olehbohdan/PrinterMonitor/images/ShaperResults/X/IMG_0770.JPG

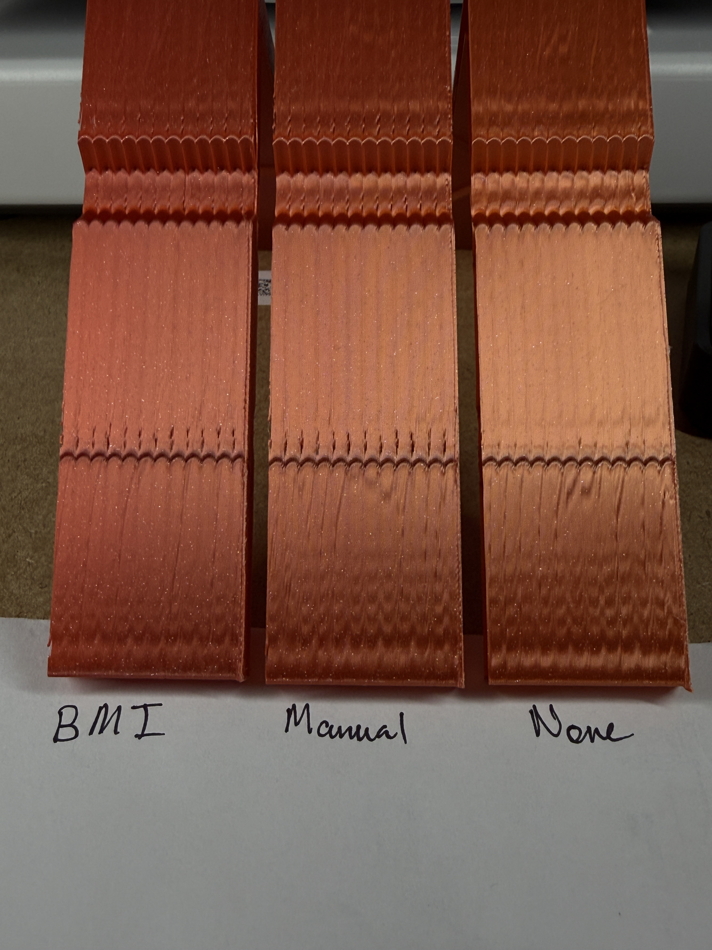
images/ShaperResults/X/IMG_0770.JPG
