olehbohdan/PrinterMonitor/images/ShaperResults/X/IMG_0772.JPG

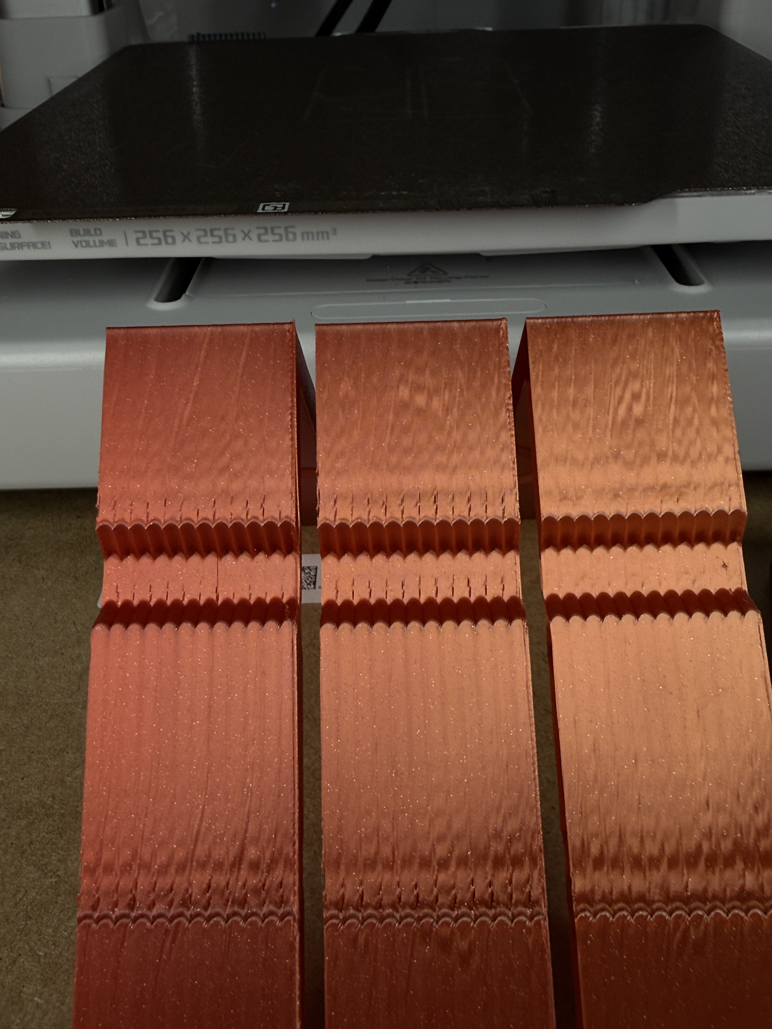
images/ShaperResults/X/IMG_0772.JPG
