olehbohdan/PrinterMonitor/images/ShaperResults/Y/IMG_0774.JPG

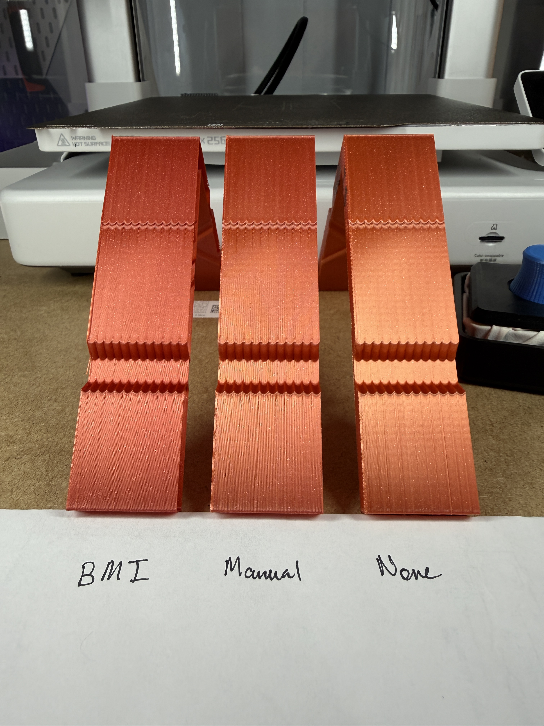
images/ShaperResults/Y/IMG_0774.JPG
