olehbohdan/PrinterMonitor/images/ShaperResults/Y/IMG_0775.JPG

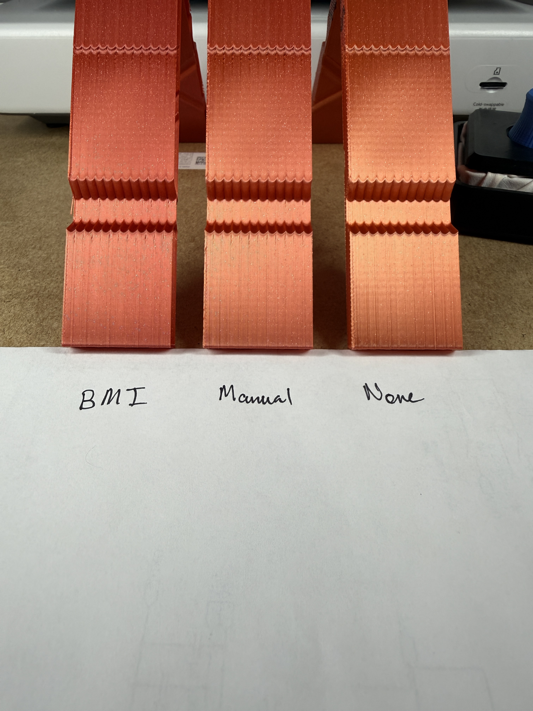
images/ShaperResults/Y/IMG_0775.JPG
