olehbohdan/PrinterMonitor/images/ShaperResults/Y/IMG_0776.JPG

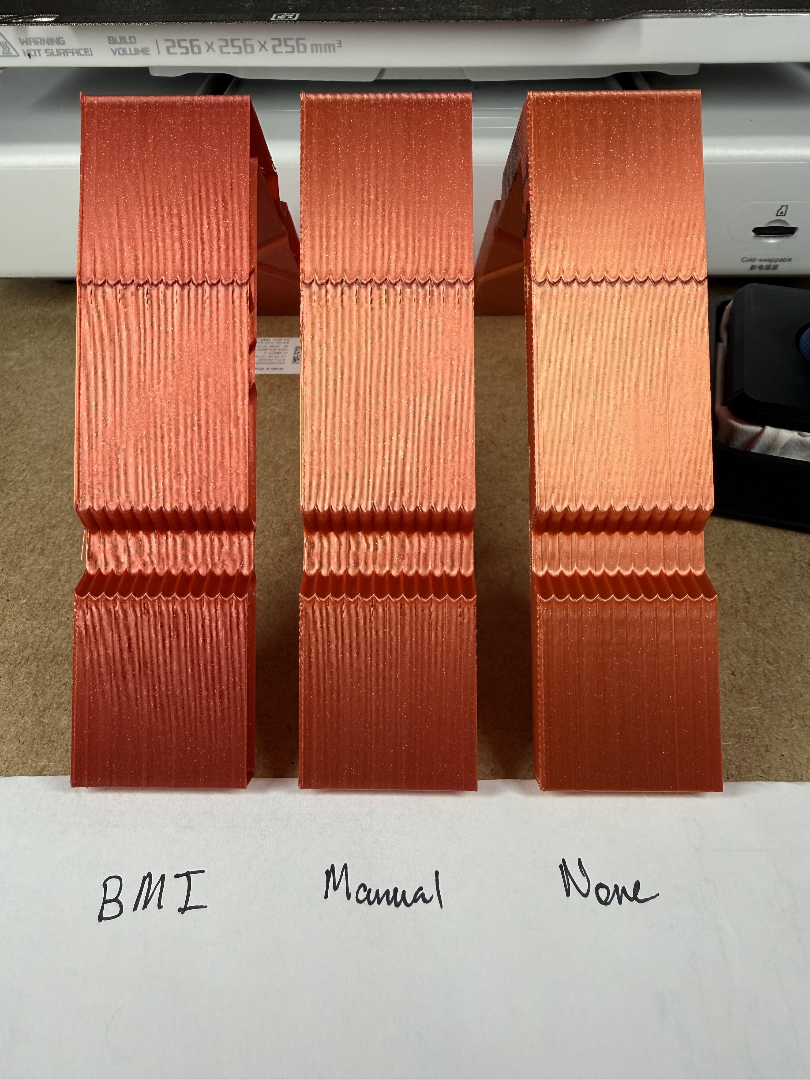
images/ShaperResults/Y/IMG_0776.JPG
